coddingtonbear/pomodoro-cube/ArduinoIDE_V2/main/display.cpp

#include "display.h"
#include "nap.h"
#include "consts.h"
#include "indicators.h"
#include "tilt.h"
#include <lvgl.h>
#include <stdio.h>
#include <string.h>
#include <Wire.h>
#include <TFT_eSPI.h>  // By Bodmer V2.5.43

// A TFT_eSPI configured for something other than this panel compiles perfectly
// and then shows nothing at all, which is a miserable thing to debug. Fail at
// build time instead: if this is not set, ArduinoIDE_V2/User_Setup.h has not
// been symlinked into the library. See the README's Building section.
#ifndef GC9A01_DRIVER
#error "TFT_eSPI is not configured for the GC9A01 -- symlink ArduinoIDE_V2/User_Setup.h into ~/Arduino/libraries/TFT_eSPI/"
#endif
#include "src/ui.h"    // SquareLine Studio generated header

// The switch-on prompt's count: Oswald at 150px, the digits 1 and 2 alone. See
// fonts/README.md.
LV_FONT_DECLARE(ui_font_FlipCount);


TFT_eSPI tft = TFT_eSPI();

static lv_disp_draw_buf_t draw_buf;

// Two bands, so LVGL draws the next one while DMA sends the last. Sixty rows
// because that is where taller stopped paying on the board: a leaning face
// redrawn in full took 124 ms in 20-row bands, 89 in 60 and 88 in 120. Each is
// under the 32K pixels a single ESP32-S3 DMA transfer can carry.
constexpr int kBandRows = 60;
static lv_color_t bandA[240 * kBandRows];
static lv_color_t bandB[240 * kBandRows];
lv_disp_drv_t disp_drv;

static bool frameOpen = false;

// Hands each band to DMA and returns at once, which LVGL takes as leave to
// start drawing into the other one. pushImageDMA() waits out the previous
// transfer before it touches the bus, so the bands queue rather than collide.
//
// The transaction is held open from the first band of a frame to the last,
// since closing it waits for DMA and would throw the overlap away. The last
// band closes it, so between frames the bus is idle and the rest of this file
// -- setRotation(), the sleep commands -- can use it without knowing about DMA.
void disp_flush(lv_disp_drv_t *disp, const lv_area_t *area, lv_color_t *color_p) {
  const int32_t w = area->x2 - area->x1 + 1;
  const int32_t h = area->y2 - area->y1 + 1;
  if (!frameOpen) {
    tft.startWrite();
    frameOpen = true;
  }
  tft.pushImageDMA(area->x1, area->y1, w, h, (uint16_t *)&color_p->full);
  if (lv_disp_flush_is_last(disp)) {
    tft.endWrite();
    frameOpen = false;
  }
  lv_disp_flush_ready(disp);
}


namespace {

// Well above hearing, so the backlight never sings, and well within what the
// LED's series resistor and the switching FET will follow.
constexpr int kBacklightFrequency = 5000;
constexpr int kBacklightBits = 8;
// Only used by the 2.x API, which allocates channels by hand. tone() takes
// channel 0, so stay at the other end.
constexpr int kBacklightChannel = 7;

bool backlightIsPwm = false;
int backlightLevel = -1;

void attachBacklightPwm() {
  if (backlightIsPwm) return;
#if ESP_ARDUINO_VERSION_MAJOR >= 3
  ledcAttach(TFT_BL_PIN, kBacklightFrequency, kBacklightBits);
#else
  ledcSetup(kBacklightChannel, kBacklightFrequency, kBacklightBits);
  Nap::keepPwmThroughSleep(kBacklightChannel, kBacklightFrequency, kBacklightBits);
  ledcAttachPin(TFT_BL_PIN, kBacklightChannel);
#endif
  backlightIsPwm = true;
}

// Hand the pin back to plain GPIO so a static level can be held through deep
// sleep. Callers set that level themselves; this only gives them the pin.
void releaseBacklightPwm() {
  if (backlightIsPwm) {
#if ESP_ARDUINO_VERSION_MAJOR >= 3
    ledcDetach(TFT_BL_PIN);
#else
    ledcDetachPin(TFT_BL_PIN);
#endif
    backlightIsPwm = false;
  }
  pinMode(TFT_BL_PIN, OUTPUT);
  backlightLevel = -1;
}

// Give back the two pads holdPausedFrame() latched. Until this runs, nothing
// written to either reaches the pin: gpio_hold_en() survives deep sleep and
// keeps holding after the wake, which is the point of it. Safe when nothing was
// held, so every path that is about to drive the backlight or the reset line
// calls it first rather than reasoning about which sleep it woke from.
void releaseHeldPins() {
  gpio_hold_dis((gpio_num_t)TFT_BL_PIN);
  gpio_hold_dis((gpio_num_t)TFT_RST);
}

// Whether tft.begin() has run this boot. A wake that decides it should go
// straight back to sleep never calls Display::setup(), and still has to be able
// to put the panel away.
bool panelBegun = false;

void beginPanelOnce() {
  if (panelBegun) return;
  tft.begin();
  tft.setRotation(0);  // Let LVGL handle software rotation
  panelBegun = true;
}

// The face last drawn, kept so a change of brightness can repaint it in the
// other scheme without the caller having to hand the timer over again.
Indicators::Ramp lastRamp = Indicators::Ramp::ToGreen;
int lastRampAt = 100;
bool lastFlow = false;
// Whether the timer last drawn was work, which is what the alarm flashes for
// once it has run out: updateTimer() has always drawn the 00:00 before
// cycleTimerFinish() takes the panel.
bool lastWork = true;
bool dimScheme = false;

// A finished timer owns the panel until something ends it, so the ordinary
// repaints stand aside rather than fighting the flash for the background.
bool alerting = false;

// The paused palette is up, and stays up through changes of brightness: a cube
// paused awake dims like any other, and the repaint that goes with dimming
// would otherwise put the running face's colours back on a stopped timer.
bool pausedFrame = false;

// Defined below, once there is an applyPalette() for it to call.
void repaintPalette();

// How the face is turned: the quarter turn the panel is set to, and the whole
// degrees LVGL is drawing on top of it.
int panelQuarter = 0;
int lean = 0;

constexpr lv_coord_t kPanelCentre = 120;

// Turn everything on the face by the lean, about the centre of the panel.
//
// The arc turns itself, by starting its sweep somewhere else. Everything else
// is drawn flat into a layer and turned on the way to the screen, about a pivot
// LVGL measures from the object's own corner -- so the pivot is the centre of
// the panel restated for each object, and has to be restated whenever one
// changes size, which a label does with its text.
void applyLean() {
  // Redraws the whole ring whether or not the angle moved, and refreshLean()
  // comes through here every second while only a label has changed size.
  const uint16_t arcRotation = (uint16_t)((lean + 360) % 360);
  if (reinterpret_cast<lv_arc_t *>(ui_Arc1)->rotation != arcRotation) {
    lv_arc_set_rotation(ui_Arc1, arcRotation);
  }

  lv_obj_update_layout(ui_Screen1);
  lv_obj_t *const leaning[] = {ui_LowBattery, ui_LowBatteryTip, ui_Countdown, ui_BankLabel};
  for (lv_obj_t *obj : leaning) {
    const lv_coord_t pivotX = kPanelCentre - obj->coords.x1;
    const lv_coord_t pivotY = kPanelCentre - obj->coords.y1;
    // Each of these invalidates the object whether or not it changed anything,
    // and most passes change only the angle.
    if (lv_obj_get_style_transform_pivot_x(obj, LV_PART_MAIN) != pivotX) {
      lv_obj_set_style_transform_pivot_x(obj, pivotX, LV_PART_MAIN);
    }
    if (lv_obj_get_style_transform_pivot_y(obj, LV_PART_MAIN) != pivotY) {
      lv_obj_set_style_transform_pivot_y(obj, pivotY, LV_PART_MAIN);
    }
    if (lv_obj_get_style_transform_angle(obj, LV_PART_MAIN) != lean * 10) {
      lv_obj_set_style_transform_angle(obj, (lv_coord_t)(lean * 10), LV_PART_MAIN);
    }
  }
}

// For whatever has just changed the size of something on a leaning face. Does
// nothing on a square one, which is every face at rest.
void refreshLean() {
  if (lean != 0) applyLean();
}

}  // namespace

void Display::finishDrawing() {
  tft.dmaWait();
}

void Display::setBacklight(int percent) {
  if (percent < 0) percent = 0;
  if (percent > 100) percent = 100;
  if (percent == backlightLevel) return;

  attachBacklightPwm();
  const uint32_t duty = (uint32_t)((percent * 255 + 50) / 100);
#if ESP_ARDUINO_VERSION_MAJOR >= 3
  ledcWrite(TFT_BL_PIN, duty);
#else
  ledcWrite(kBacklightChannel, duty);
#endif
  backlightLevel = percent;

  // Dropping the backlight also swaps the scheme: at this brightness a field of
  // colour reads where a thin arc does not. Repaint only on the crossing, so
  // the every-20ms call in loop() stays free.
  const bool dim = percent < BACKLIGHT_FULL_PERCENT;
  if (dim != dimScheme) {
    dimScheme = dim;
    repaintPalette();
  }
}

// LVGL's own image drawing, which drawTransformedWithoutAa() stands in front of.
static void (*drawImgDecoded)(lv_draw_ctx_t *, const lv_draw_img_dsc_t *, const lv_area_t *,
                              const uint8_t *, lv_img_cf_t) = nullptr;

// A leaning face is its labels drawn flat into a layer and then turned, and
// the turn was the bulk of every frame drawn at an angle. Turned without
// anti-aliasing it samples the nearest pixel rather than blending four, at the
// cost of stepped edges on the digits while the cube is off square.
//
// Only transformed draws are touched: the display's own antialiasing flag
// would have done the same for them, but it also rounds off every glyph and
// arc on the panel, square or not.
static void drawTransformedWithoutAa(lv_draw_ctx_t *ctx, const lv_draw_img_dsc_t *dsc,
                                     const lv_area_t *coords, const uint8_t *map, lv_img_cf_t cf) {
  if (dsc->angle == 0 && dsc->zoom == LV_IMG_ZOOM_NONE) {
    drawImgDecoded(ctx, dsc, coords, map, cf);
    return;
  }
  lv_draw_img_dsc_t hard = *dsc;
  hard.antialias = 0;
  drawImgDecoded(ctx, &hard, coords, map, cf);
}

// Whether setup() has run this boot. A switched-off cube brings the panel up to
// count the flips down, and switching it on can then go on to draw a paused
// frame, which asks again; LVGL cannot be initialised twice.
bool displayUp = false;

// The screen showMessage() and showFlipsToGo() put up, while it is up: the text
// of a message or the caption under the count, and the count itself, which is
// hidden for a message.
lv_obj_t *messageScreen = nullptr;
lv_obj_t *messageLabel = nullptr;
lv_obj_t *figureLabel = nullptr;
bool messageInverted = false;

// Push whatever LVGL has pending to the panel now, for the paths that are about
// to block or sleep rather than return to a loop() that would do it.
void pumpLvgl() {
  for (int i = 0; i < 4; i++) {
    Display::render();
    delay(20);
  }
}

void Display::render() {
  // LVGL keeps time only by what it is told. It was told 20 ms a pass, which
  // was true only while a pass was just the delay: once drawing a leaning face
  // took 90 ms of its own, LVGL still saw 20 go by, found its 30 ms refresh
  // period not yet up, and skipped every other pass -- so a frame came about
  // once per two passes plus the drawing, rather than once per pass.
  static uint32_t lastTick = millis();
  const uint32_t now = millis();
  lv_tick_inc(now - lastTick);
  lastTick = now;
  lv_timer_handler();
}

void Display::setup() {
  if (displayUp) return;
  displayUp = true;

  // A paused sleep locks the backlight and the panel's reset line on through
  // deep sleep; release both before driving them again, or tft.begin() cannot
  // reset the panel.
  releaseHeldPins();
  releaseBacklightPwm();
  // Dark until the glass has been wiped. The GC9A01 keeps its frame memory
  // through sleep-in, and through the reset begin() gives it, so bringing the
  // panel up under a lit backlight showed whatever was last drawn before the
  // cube slept -- for the moment it takes LVGL to draw over it.
  digitalWrite(TFT_BL_PIN, LOW);
  // Initialize TFT
  beginPanelOnce();
  tft.fillScreen(TFT_BLACK);
  tft.initDMA();

  // Initialize LVGL
  lv_init();
  lv_disp_draw_buf_init(&draw_buf, bandA, bandB, 240 * kBandRows);
  lv_disp_drv_init(&disp_drv);
  disp_drv.hor_res = 240;
  disp_drv.ver_res = 240;
  disp_drv.flush_cb = disp_flush;
  disp_drv.draw_buf = &draw_buf;

  lv_disp_t *const disp = lv_disp_drv_register(&disp_drv);
  // loop() is what paces redraws, a pass at least LOOP_PASS_MS apart, so LVGL
  // should draw whenever a pass asks. Its own default of 30 ms skipped every
  // other pass once a frame at an angle came in under that.
  lv_timer_set_period(disp->refr_timer, LOOP_PASS_MS / 2);
  drawImgDecoded = disp->driver->draw_ctx->draw_img_decoded;
  disp->driver->draw_ctx->draw_img_decoded = drawTransformedWithoutAa;

  ui_init();

  // PWM only once TFT_eSPI has finished with the pin. It leaves TFT_BL alone
  // unless TFT_BACKLIGHT_ON is defined, which tft_setup.h does not define -- but
  // an LEDC channel it did clobber would be silently stuck, and attaching after
  // begin() costs nothing to rule that out.
  //
  // At nothing, and after the face exists, since a change of level repaints
  // it. Whoever draws the first frame lights it: loop() does at the end of
  // every pass, and the paths that never reach loop() do for themselves.
  // Wiping the glass first was not enough on the board, where the last frame
  // still showed for a moment.
  Display::setBacklight(0);
}


// Checked first for the same reason as the style setters below: showing an
// object redraws the whole of it even when it was already showing, and the
// arc's whole is most of the panel.
static void show(lv_obj_t *obj, bool visible) {
  if (visible == !lv_obj_has_flag(obj, LV_OBJ_FLAG_HIDDEN)) return;
  if (visible) lv_obj_clear_flag(obj, LV_OBJ_FLAG_HIDDEN);
  else lv_obj_add_flag(obj, LV_OBJ_FLAG_HIDDEN);
}

void Display::updateBattery(float voltage) {
  // Printed with %d rather than %.2f: lv_snprintf only handles floats when
  // LV_SPRINTF_USE_FLOAT is set, which is off by default and lives in an
  // lv_conf.h this repo doesn't control.
  const int centivolts = (int)(voltage * 100.0f + 0.5f);
  lv_label_set_text_fmt(ui_LowBatteryVoltage, "%d.%02d", centivolts / 100, centivolts % 100);

  // Nothing on screen at all until the charge is actually worth acting on.
  const bool warn = Indicators::showLowBattery(voltage);
  show(ui_LowBattery, warn);
  show(ui_LowBatteryTip, warn);
  refreshLean();
}

// Style setters that leave an object alone when it already has the value.
//
// LVGL redraws an object whenever one of its styles is set, whether or not the
// value changed, and the face is repainted from scratch every second. Setting
// the screen's background that way redrew all 240x240 pixels once a second, a
// frame that takes long enough to cross the SPI bus that it could be seen
// arriving in bands. Skipping the no-ops leaves the tick redrawing only the
// digits and the part of the arc that moved.
static void setColor(lv_obj_t *obj, lv_style_prop_t prop, uint32_t color, lv_part_t part) {
  const lv_color_t c = lv_color_hex(color);
  if (lv_obj_get_style_prop(obj, part, prop).color.full == c.full) return;
  lv_style_value_t v;
  v.color = c;
  lv_obj_set_local_style_prop(obj, prop, v, part);
}

static void setOpa(lv_obj_t *obj, lv_style_prop_t prop, lv_opa_t opa, lv_part_t part) {
  if (lv_obj_get_style_prop(obj, part, prop).num == opa) return;
  lv_style_value_t v;
  v.num = opa;
  lv_obj_set_local_style_prop(obj, prop, v, part);
}

// Paint the arc and its knob in one colour, at one opacity.
static void setArcAppearance(uint32_t color, lv_opa_t opa) {
  setColor(ui_Arc1, LV_STYLE_ARC_COLOR, color, LV_PART_INDICATOR);
  setOpa(ui_Arc1, LV_STYLE_ARC_OPA, opa, LV_PART_INDICATOR);
  setColor(ui_Arc1, LV_STYLE_BG_COLOR, color, LV_PART_KNOB);
  setOpa(ui_Arc1, LV_STYLE_BG_OPA, opa, LV_PART_KNOB);
}

// The low-battery outline is three objects with three different style
// properties, which is why it needs its own pass rather than joining the labels.
static void setBatteryColor(uint32_t color) {
  setColor(ui_LowBattery, LV_STYLE_BORDER_COLOR, color, LV_PART_MAIN);
  setColor(ui_LowBatteryTip, LV_STYLE_BG_COLOR, color, LV_PART_MAIN);
  setColor(ui_LowBatteryVoltage, LV_STYLE_TEXT_COLOR, color, LV_PART_MAIN);
}

// Paint every colour on the panel at once, so a swap can't half-apply.
static void applyPalette(const Indicators::Palette &p) {
  setColor(ui_Screen1, LV_STYLE_BG_COLOR, p.background, LV_PART_MAIN);
  setColor(ui_Arc1, LV_STYLE_ARC_COLOR, p.track, LV_PART_MAIN);
  lv_obj_t *const labels[] = {ui_Countdown, ui_BankLabel};
  for (lv_obj_t *label : labels) {
    setColor(label, LV_STYLE_TEXT_COLOR, p.text, LV_PART_MAIN);
  }
  setArcAppearance(p.arc, LV_OPA_COVER);
  setBatteryColor(p.battery);
}

namespace {

void repaintPalette() {
  if (alerting || pausedFrame) return;
  applyPalette(Indicators::palette(lastRamp, lastRampAt, lastFlow, dimScheme));
}

}  // namespace

void Display::deepSleep() {
  // Both of these were no-ops when the last sleep held a frame: the pads were
  // still latched, so the backlight stayed on at full for the whole of the next
  // sleep. A cube parked face up and then turned face down went dark on the
  // outside and burned the pack on the inside.
  releaseHeldPins();
  releaseBacklightPwm();
  digitalWrite(TFT_BL_PIN, LOW);
  // Reached on a wake that went straight back to sleep without ever bringing
  // the display up, in which case there is no SPI to send a command over yet --
  // and a panel left holding a frame is still refreshing one, at a few
  // milliamps, which is an order above what the rest of the cube draws asleep.
  // The backlight is already off, so none of this is seen.
  beginPanelOnce();
  // Send GC9A01 Sleep In command
  tft.writecommand(0x10);
  delay(120); // Required transition delay for the controller to power down
}

void Display::holdPausedFrame() {
  // No Sleep In command: the panel keeps refreshing the frame from its own
  // memory, and holding the pin keeps it lit once the CPU stops.
  //
  // The reset line has to be held too. esp_deep_sleep_start() returns every pad
  // that is not held to its default -- high impedance -- and a floating RST on
  // the GC9A01 drifts low within seconds, which resets the controller, clears
  // its frame memory and drops it back into sleep-in. That is what blanked the
  // paused frame a few seconds after the cube was set down: the backlight was
  // still on, there was just nothing left on the panel to light.
  //
  // Full brightness, not the idle level, and not a choice: nothing is left
  // running to generate PWM once the CPU stops, and gpio_hold_en() freezes the
  // instantaneous level rather than the duty cycle. A parked cube is therefore
  // lit at full or not at all -- turning it face down is how you turn it off.
  // Deliberately does *not* release the holds first. When they are already on,
  // they are already holding exactly the levels this function is about to ask
  // for, so releasing them buys nothing -- and it hands the reset line back to
  // an output register that waking from deep sleep has cleared to zero. The pad
  // then presents a LOW for as long as it takes to get round to writing it
  // again, which is a reset pulse: the GC9A01 clears its frame memory and drops
  // into sleep-in, and the backlight goes on being held up over a blank panel.
  // That is the same symptom the held reset line was introduced to fix, put
  // back by the release that was supposed to make this path safe.
  releaseBacklightPwm();
  digitalWrite(TFT_BL_PIN, HIGH);
  gpio_hold_en((gpio_num_t)TFT_BL_PIN);

  // Level before direction, for the same reason: this writes the output
  // register while the pad is still an input, so changing the direction takes
  // it straight to HIGH rather than through whatever the register held.
  digitalWrite(TFT_RST, HIGH);
  pinMode(TFT_RST, OUTPUT);
  gpio_hold_en((gpio_num_t)TFT_RST);
}

void Display::showPaused() {
  // Back to the dark palette whether the pause caught a countdown or a flow
  // stint, and whether the panel was dim or bright: paused has to look like one
  // thing, awake and dimmed or asleep and held at full. Neither has any
  // business with a half-finished flash, which would otherwise be the frame
  // left lit on the panel for as long as the cube sits there.
  alerting = false;
  pausedFrame = true;
  show(ui_Arc1, true);
  applyPalette({SCREEN_BG_COLOR, COUNTDOWN_COLOR_PAUSED, ARC_COLOR_PAUSED, ARC_TRACK_COLOR,
                LOW_BATTERY_COLOR});

  // The frame has to reach the panel before the CPU stops, so pump LVGL rather
  // than waiting for the next loop() that will never come.
  pumpLvgl();
}

// Puts the message screen up if it is not already. A screen of its own rather
// than labels over the face: nothing of the timer belongs on it, and dropping it
// afterwards leaves the face as it was.
void ensureMessageScreen() {
  Display::setup();
  if (messageScreen) return;
  messageScreen = lv_obj_create(NULL);
  lv_obj_set_style_bg_opa(messageScreen, LV_OPA_COVER, LV_PART_MAIN);

  messageLabel = lv_label_create(messageScreen);
  lv_obj_set_style_text_font(messageLabel, &lv_font_montserrat_20, LV_PART_MAIN);
  lv_obj_set_style_text_align(messageLabel, LV_TEXT_ALIGN_CENTER, LV_PART_MAIN);
  lv_label_set_text(messageLabel, "");

  figureLabel = lv_label_create(messageScreen);
  lv_obj_set_style_text_font(figureLabel, &ui_font_FlipCount, LV_PART_MAIN);
  lv_label_set_text(figureLabel, "");
  lv_obj_add_flag(figureLabel, LV_OBJ_FLAG_HIDDEN);

  lv_scr_load(messageScreen);
}

// Colours the message screen and pushes it out. Nothing is running loop()
// while one of these is up, so the frame has to be pushed out here or it never
// reaches the glass.
void presentMessageScreen(bool inverted) {
  messageInverted = inverted;
  const lv_color_t bg = inverted ? lv_color_white() : lv_color_black();
  const lv_color_t fg = inverted ? lv_color_black() : lv_color_white();
  lv_obj_set_style_bg_color(messageScreen, bg, LV_PART_MAIN);
  lv_obj_set_style_text_color(messageLabel, fg, LV_PART_MAIN);
  lv_obj_set_style_text_color(figureLabel, fg, LV_PART_MAIN);
  pumpLvgl();
  Display::setBacklight(BACKLIGHT_FULL_PERCENT);
}

void Display::showMessage(const char *text, bool inverted) {
  ensureMessageScreen();
  const bool figureShown = !lv_obj_has_flag(figureLabel, LV_OBJ_FLAG_HIDDEN);
  if (!figureShown && strcmp(lv_label_get_text(messageLabel), text) == 0 &&
      messageInverted == inverted) {
    return;
  }

  lv_obj_add_flag(figureLabel, LV_OBJ_FLAG_HIDDEN);
  lv_label_set_text(messageLabel, text);
  lv_obj_center(messageLabel);
  presentMessageScreen(inverted);
}

void Display::showFlipsToGo(int flips) {
  ensureMessageScreen();
  char figure[12];
  snprintf(figure, sizeof figure, "%d", flips);
  const bool figureShown = !lv_obj_has_flag(figureLabel, LV_OBJ_FLAG_HIDDEN);
  if (figureShown && strcmp(lv_label_get_text(figureLabel), figure) == 0 && !messageInverted) {
    return;
  }

  // The figure a little above centre and the caption under it, so the pair sits
  // centred on the round panel together rather than the figure alone.
  lv_obj_clear_flag(figureLabel, LV_OBJ_FLAG_HIDDEN);
  lv_label_set_text(figureLabel, figure);
  lv_obj_align(figureLabel, LV_ALIGN_CENTER, 0, -22);
  lv_label_set_text(messageLabel, "to go");
  lv_obj_align_to(messageLabel, figureLabel, LV_ALIGN_OUT_BOTTOM_MID, 0, 8);
  presentMessageScreen(false);
}

void Display::hideMessage() {
  if (!messageScreen) return;
  lv_scr_load(ui_Screen1);
  lv_obj_del(messageScreen);
  messageScreen = nullptr;
  messageLabel = nullptr;
  figureLabel = nullptr;
}

void Display::setAngle(float degrees) {
  const Tilt::Split split = Tilt::split(degrees);

  if (split.quarter != panelQuarter) {
    panelQuarter = split.quarter;
    // Changes where writes land, not what is already on the glass, so the old
    // frame stands until the new one is drawn over it.
    tft.setRotation(split.quarter);
    lv_obj_invalidate(lv_scr_act());
  }

  if (split.lean != lean) {
    lean = split.lean;
    applyLean();
  }
}

void Display::rotateScreen(Orientation ori) {
  Display::setAngle(Tilt::faceAngle(ori));
}

static void setCountdownText(int seconds) {
  lv_label_set_text(ui_Countdown, Indicators::clockText(seconds).text);
}

// The bank in the smallest form that stays unambiguous: no marker to explain,
// because minutes and seconds are shown as such and hours only appear when
// there are some.
static void setBankText(int seconds) {
  if (seconds < 0) seconds = 0;
  if (seconds >= 3600) {
    lv_label_set_text_fmt(ui_BankLabel, "BANK %d:%02d:%02d", seconds / 3600,
                          (seconds % 3600) / 60, seconds % 60);
  } else {
    lv_label_set_text_fmt(ui_BankLabel, "BANK %d:%02d", seconds / 60, seconds % 60);
  }
}

void Display::updateTimer(const TimerView &view) {
  // Whatever brought us here ended the alarm: a new face, or a timer with
  // seconds on it again. Take the ring back before anything is painted.
  alerting = false;
  pausedFrame = false;
  show(ui_Arc1, true);

  setCountdownText(view.seconds);

  // The bank belongs on the work face: on the break face the big number already
  // is the bank, counting down.
  const bool showBank = view.flow && view.countingUp;
  if (showBank) setBankText(view.bankSeconds);
  show(ui_BankLabel, showBank);

  // Counting up has no total to drain against, so the arc fills as a lap
  // indicator, its colour running the ramp over what is left of the lap.
  const int remaining = view.countingUp ? Indicators::lapPercent(view.seconds)
                                        : Indicators::remainingPercent(view.seconds, view.selSeconds);
  lastRamp = Indicators::rampFor(view.work, view.countingUp, view.seconds);
  lastRampAt = view.countingUp ? 100 - remaining : remaining;
  lastFlow = view.flow;
  lastWork = view.work;
  lv_arc_set_value(ui_Arc1, remaining);

  // Repaints every colour from scratch, which also undoes showPaused() without
  // needing to know whether it ran.
  repaintPalette();

  refreshLean();
}

unsigned long lastFinishChange = 0;
bool finishInverted = false;

void Display::cycleTimerFinish() {
  const unsigned long now = millis();

  // Called every pass while the timer sits at zero, and self-timed, so the
  // flash keeps its own cadence rather than the motor's.
  if (alerting) {
    if (now - lastFinishChange < (unsigned long)ALERT_FLASH_MS) return;
    finishInverted = !finishInverted;
  } else {
    // First pass of an alarm: take the panel, and start on the dark half so the
    // flash reads as something arriving rather than something leaving.
    alerting = true;
    finishInverted = false;
    show(ui_Arc1, false);
  }

  applyPalette(Indicators::alertPalette(finishInverted, lastWork));
  lastFinishChange = now;
}
