coddingtonbear/pomodoro-cube/ArduinoIDE_V2/main/ble.h

#pragma once
#include "bthome.h"

// The radio half of the BTHome broadcast: takes the payload bthome.cpp builds
// and puts it on the air over NimBLE.
//
// Advertising only -- there is no GATT server, no scanning and nothing to
// connect to. A BTHome device is a beacon, and a non-connectable advertisement
// is a millisecond of radio at a time, sent in short bursts.
namespace BLE {

// Puts the cube on the air. The controller itself is brought up by the first
// burst and stays up until shutdown(); only advertising starts and stops with
// each burst. Bringing it up blocks while the NimBLE host syncs, which the
// trace reports.
void setup();

// Offer the current state. Cheap enough to call on every pass of the loop: the
// radio only goes on the air when BTHome::Scheduler says a burst is due, and
// this is also what takes it off again once the burst has run. Does nothing
// before setup().
void publish(const BTHome::State &state);

// Puts the advertisement that goes out as the cube falls asleep on the air,
// with connectivity and running both dropped -- see
// BTHome::Sequencer::farewell() -- at the fastest interval a legacy
// advertisement allows, and returns at once. The radio keeps repeating it
// through whatever shutdown work follows, until shutdown() is called; the
// farewell cannot be repeated later, so every copy that gets out is one the
// receiver might not otherwise have heard.
//
// Safe to call when BLE was never brought up, which is the path a cube takes
// when it wakes on a resting face and goes straight back to sleep.
void farewell();

// Shuts the controller down. Call it last, immediately before deep sleep: it
// first makes sure a farewell put on the air by farewell() has had at least
// FAREWELL_MIN_AIRTIME_MS to repeat, blocking for the remainder if the work in
// between was quicker than that, so the guarantee does not depend on how long
// the panel and motor happen to take. Deep sleep cuts the radio's power
// anyway; shutting it down in order means the controller is not
// mid-transmission when that happens.
//
// Safe to call when BLE was never brought up.
void shutdown();

// Whether a burst or the farewell is on the air. The CPU does not light-sleep
// under one -- the controller is built without the sleep support that would
// let advertising and light sleep coexist.
bool onAir();

// The least time a farewell is on the air before shutdown() lets the radio go.
// The shutdown work it overlaps -- putting the panel away, the second's pause,
// the shutdown buzz -- takes longer than this in practice; the figure is a
// floor, not the expectation.
constexpr unsigned long FAREWELL_MIN_AIRTIME_MS = 1000;

}  // namespace BLE
