coddingtonbear/pomodoro-cube/ArduinoIDE_V2/main/util.cpp

#include "util.h"
#include <Arduino.h>
#include <math.h>
#include "consts.h"
#include "battery.h"
#include "util.h"
#include "qmi.h"
#include "display.h"
#include <driver/rtc_io.h>
#include "vFilter.h"
#include "haptic.h"
#include "ble.h"

VoltageSmoother<10> vFilter;


void Util::updateBattery() {
  vFilter.add(Battery::getVoltage());
  Display::updateBattery(vFilter.getAverage());
}

float Util::batteryVolts() {
  return vFilter.getAverage();
}

Orientation Util::calcOrientation(float ax, float ay, float az) {
  // Whichever axis carries the most of gravity names the face. The signs are
  // verified on hardware: the QMI8658's +Z points into the back of the cube,
  // not out of the front, so a cube resting screen-up reads -1g on Z.
  //
  // This used to test each axis against a fixed +-0.8, and fall through to
  // DEG_0 when nothing matched. That left a dead zone covering every attitude
  // more than about 37 degrees off an axis, and the fall-through reported a
  // timer face rather than admitting it did not know -- so a board resting at
  // an angle ran a 25-minute timer it had never been put on. In a
  // fifteen-minute trace from the board, 38.8% of all samples landed in that
  // dead zone. A dominant axis has no dead zone: every reading names a face,
  // and readings too close to call are screened out by isDecisive() instead of
  // being quietly answered wrong.
  const float mx = fabsf(ax);
  const float my = fabsf(ay);
  const float mz = fabsf(az);

  if (mz >= mx && mz >= my) return az > 0 ? Orientation::FACE_DOWN : Orientation::FACE_UP;
  if (mx >= my) return ax > 0 ? Orientation::DEG_180 : Orientation::DEG_0;
  return ay > 0 ? Orientation::DEG_270 : Orientation::DEG_90;
}

bool Util::isGravityOnly(float ax, float ay, float az) {
  const float magnitude = sqrtf(ax * ax + ay * ay + az * az);
  return magnitude >= ORI_GRAVITY_MIN_G && magnitude <= ORI_GRAVITY_MAX_G;
}

bool Util::isDecisive(float ax, float ay, float az) {
  float mx = fabsf(ax);
  float my = fabsf(ay);
  float mz = fabsf(az);

  // The top two, without sorting all three.
  float first = mx, second = my;
  if (second > first) { const float swap = first; first = second; second = swap; }
  if (mz > first) { second = first; first = mz; }
  else if (mz > second) { second = mz; }

  return first - second >= ORI_DOMINANCE_MARGIN_G;
}


void Util::deepSleep(SleepMode mode, bool announce) {
  // Before anything else that takes time: Home Assistant holds the last state
  // it heard, so a cube that just stopped counting has to say so while it still
  // has a radio. This only puts the farewell on the air; the radio goes on
  // repeating it through everything below and is shut down last, so the
  // second's pause doubles as airtime for the one advertisement that cannot be
  // sent again.
  BLE::farewell();

  // Whatever the motor was part-way through ends here: nothing below returns to
  // loop() to finish it, and a motor left running would be the movement that
  // wakes the cube straight back up.
  Haptic::stop();

  // Ahead of the pause below rather than after it, so the motor has that second
  // to spin down before the wake-on-motion detector is armed.
  if (announce) Haptic::playBlocking(Haptic::Pattern::FaceChange);

  // Written down rather than worked out again on the next wake. A wake that
  // goes straight back to sleep never brings the panel up, so it cannot ask the
  // panel what it is showing -- and the two answers need different handling:
  // a held frame has to be put away before the panel can go dark, and a blank
  // panel has to be drawn on before the backlight is worth holding up.
  RtcState::data().panelHoldingFrame = (mode == SleepMode::Paused);

  if (mode == SleepMode::Off) Display::deepSleep();
  else Display::holdPausedFrame();

  delay(1000);

  QMI::setupWakeup();

  // Float I2C lines to prevent parasitic draw
  pinMode(I2C_SDA_PIN, INPUT);
  pinMode(I2C_SCL_PIN, INPUT);

  rtc_gpio_pullup_dis(IMU_INT_PIN);
  rtc_gpio_pulldown_en(IMU_INT_PIN);

  esp_sleep_enable_ext0_wakeup(IMU_INT_PIN, 1);  // 1 = Wakeup at HIGH

  Haptic::holdForSleep();

  // Last, so the farewell has had the whole of the above to repeat.
  BLE::shutdown();

  esp_deep_sleep_start();
}

bool Util::isRestingFace(Orientation ori) {
  return ori == Orientation::FACE_UP || ori == Orientation::FACE_DOWN;
}

Util::RestPlan Util::restOnFace(RtcState::Data &data, Orientation ori, Orientation timerFace,
                                int remaining, int selected, bool countingUp) {
  // Park rather than discard, on either face. Setting the cube down is not the
  // same as choosing a different interval -- that is what standing it on another
  // face means -- so the pause and the break bank both survive it. Face down is
  // face up with the lights out.
  RtcState::storePause(data, timerFace, remaining, selected, countingUp);

  // Face down is also off, which is the one thing that tells the two faces
  // apart after the lights: a cube put away face down stays down until it is
  // deliberately switched back on, however much it is jostled.
  const bool lit = ori == Orientation::FACE_UP;
  data.switchedOff = !lit;
  return {lit, lit ? SleepMode::Paused : SleepMode::Off};
}

void Util::parkFreshTimer(RtcState::Data &data) {
  if (RtcState::hasPause(data)) return;
  RtcState::storePause(data, Orientation::DEG_0, TIMER_WORK_SECONDS, TIMER_WORK_SECONDS, false);
}

int Util::backlightPercent(const BacklightView &view) {
  // Just set down. The face was chosen a moment ago, and what it came up with is
  // the answer to that choice.
  if (view.sinceFaceChangeMs < (unsigned long)BACKLIGHT_ATTENTION_SECONDS * 1000UL) {
    return BACKLIGHT_FULL_PERCENT;
  }

  // Just tapped, which is the same request made deliberately: someone wants to
  // read a face that has settled to the idle level. Held longer than a face
  // change, because they are coming to it cold rather than already looking.
  if (view.sinceTapMs < (unsigned long)BACKLIGHT_TAP_SECONDS * 1000UL) {
    return BACKLIGHT_FULL_PERCENT;
  }

  // Running out, or run out. The same test covers both: a countdown at 0 has
  // finished and is buzzing, and stays lit until it is dealt with -- which is
  // bounded, because a finished timer sleeps the cube after thirty seconds.
  //
  // Not while paused: a countdown parked with four seconds left is not about
  // to do anything, and would otherwise hold the panel at full for as long as
  // it lay there.
  if (!view.paused && !view.countingUp &&
      view.remainingSeconds <= BACKLIGHT_ATTENTION_SECONDS) {
    return BACKLIGHT_FULL_PERCENT;
  }

  // A flow lap closing, from a moment before to a moment after: the arc comes
  // round, a pomodoro is scored, and the colour snaps to the next lap's. Not
  // the start of the first lap, which is no closing at all -- and is lit
  // anyway, as the face change it is.
  if (!view.paused && view.countingUp && view.remainingSeconds >= 0) {
    const unsigned long lapMs = (unsigned long)FLOW_LAP_SECONDS * 1000UL;
    const unsigned long elapsedMs = (unsigned long)view.remainingSeconds * 1000UL +
                                    (view.sinceTickMs < 1000UL ? view.sinceTickMs : 999UL);
    const unsigned long intoLap = elapsedMs % lapMs;
    const bool closing = intoLap >= lapMs - BACKLIGHT_LAP_MS;
    const bool closed = elapsedMs >= lapMs && intoLap < BACKLIGHT_LAP_MS;
    if (closing || closed) return BACKLIGHT_FULL_PERCENT;
  }

  return BACKLIGHT_IDLE_PERCENT;
}

uint32_t Util::cpuMhz(int backlightPercent) {
  return backlightPercent >= BACKLIGHT_FULL_PERCENT ? CPU_MHZ_LIT : CPU_MHZ_IDLE;
}

bool Util::loopIsIdle(const PaceView &view) {
  // Lit is when someone is looking, and the angle is being followed at the
  // rate it was tuned for; busy is timing that is finer than an idle pass.
  return view.backlightPercent < BACKLIGHT_FULL_PERCENT && !view.busy &&
         view.sinceMovedMs >= LOOP_STILL_HOLD_MS;
}

uint32_t Util::loopPassMs(const PaceView &view) {
  if (!loopIsIdle(view)) return LOOP_PASS_MS;
  // On the tick rather than late for it. At least a millisecond, so a tick
  // that is due now is taken by the very next pass.
  if (view.untilTickMs < LOOP_IDLE_PASS_MS) {
    return view.untilTickMs == 0 ? 1 : (uint32_t)view.untilTickMs;
  }
  return LOOP_IDLE_PASS_MS;
}

Util::TimerSpec Util::getTimerSpec(Orientation ori, int bankedBreakSeconds) {
  switch (ori) {
    case Orientation::DEG_0:
      return {TimerKind::Work, TimerMode::Countdown, TIMER_WORK_SECONDS, false, false};
    case Orientation::DEG_90:
      return {TimerKind::Break, TimerMode::Countdown, TIMER_SHORT_BREAK_SECONDS, false, false};
    case Orientation::DEG_180:
      // Flow's work face: no length, because it counts up until the cube is
      // turned off it.
      return {TimerKind::Work, TimerMode::CountUp, 0, true, false};
    case Orientation::DEG_270:
      // Flow's break face pays out the bank and nothing else. An empty bank is
      // a break of no length, which finishes the moment it starts -- there is
      // nothing to fall back on, because any fallback would be break time
      // nobody worked for.
      return {TimerKind::Break, TimerMode::Countdown,
              bankedBreakSeconds > 0 ? bankedBreakSeconds : 0, true, true};
    default:
      // A resting face runs no timer, but must still not report zero: a
      // zero-length timer would divide by zero in the arc.
      return {TimerKind::Work, TimerMode::Countdown, TIMER_WORK_SECONDS, false, false};
  }
}

int Util::flowBreakCredit(int workedSeconds) {
  if (workedSeconds <= 0) return 0;
  return workedSeconds / FLOW_BREAK_DIVISOR;
}

int Util::flowBankPreview(int bankedSeconds, int elapsedSeconds) {
  if (bankedSeconds < 0) bankedSeconds = 0;
  return bankedSeconds + flowBreakCredit(elapsedSeconds);
}

bool Util::completesFlowLap(int elapsedSeconds) {
  return elapsedSeconds > 0 && elapsedSeconds % FLOW_LAP_SECONDS == 0;
}

Util::SwitchOnListener::SwitchOnListener(unsigned long nowMs)
    : deadline_(nowMs + SWITCH_ON_FLIP_WINDOW_MS), lastDisturbed_(nowMs) {}

Util::SwitchOnListener::Side Util::SwitchOnListener::sideOf(float ax, float ay, float az) {
  const float magnitude = sqrtf(ax * ax + ay * ay + az * az);
  if (magnitude < FLIP_MAGNITUDE_MIN_G || magnitude > FLIP_MAGNITUDE_MAX_G) return Side::Neither;
  // +Z points into the back of the cube; see calcOrientation().
  if (az <= -FLIP_SIDE_MIN_G) return Side::Up;
  if (az >= FLIP_SIDE_MIN_G) return Side::Down;
  return Side::Neither;
}

Util::SwitchOnVerdict Util::SwitchOnListener::update(bool haveReading, float ax, float ay,
                                                     float az, unsigned long nowMs) {
  if (haveReading) {
    updateOriDebounce(ax, ay, az, nowMs);

    // A side counts once it has held for FLIP_HOLD_MS, and a flip is the cube
    // coming to face up from face down. Going face up again without having
    // been face down in between is not another flip, and nor is a side face:
    // standing the cube on a timer face and back is a quarter turn, not a flip.
    const Side reading = sideOf(ax, ay, az);
    if (reading != candidate_) {
      candidate_ = reading;
      candidateSince_ = nowMs;
    } else if (reading != Side::Neither && reading != side_ &&
               nowMs - candidateSince_ >= FLIP_HOLD_MS) {
      side_ = reading;
      if (side_ == Side::Up) {
        if (++flips_ >= SWITCH_ON_FLIPS) return SwitchOnVerdict::On;
        deadline_ = nowMs + SWITCH_ON_FLIP_WINDOW_MS;
      }
    }
  }

  const Orientation face = getDebouncedOriState();
  const bool resting = haveReading && isGravityOnly(ax, ay, az) &&
                       calcOrientation(ax, ay, az) == face;
  if (!resting) lastDisturbed_ = nowMs;

  // Left lying on some other face before it was ever flipped: not being
  // switched on, so no reason to wait out the window.
  if (flips_ == 0 && face != Orientation::FACE_UP && face != Orientation::UNDEFINED &&
      nowMs - lastDisturbed_ >= SWITCH_ON_GIVE_UP_MS) {
    return SwitchOnVerdict::StayOff;
  }
  if ((long)(nowMs - deadline_) >= 0) return SwitchOnVerdict::StayOff;
  return SwitchOnVerdict::Listening;
}

// The face the cube is currently being read as, and the one it has been read as
// for long enough to believe.
Orientation candidateState = Orientation::UNDEFINED;
unsigned long candidateSince = 0;
Orientation debouncedState = Orientation::UNDEFINED;

bool Util::updateOriDebounce(float ax, float ay, float az, unsigned long nowMs) {
  Orientation rawState = Orientation::UNDEFINED;
  if (isGravityOnly(ax, ay, az)) {
    const Orientation face = calcOrientation(ax, ay, az);
    // An attitude poised between two faces may go on confirming the face the
    // cube is already believed to be on, but is never enough to move it onto a
    // new one. UNDEFINED here means "no opinion", which restarts the clock
    // below rather than being accepted as a face of its own.
    //
    // Unless no face is believed yet, in which case the best available answer
    // is taken however narrow its lead. The margin exists to stop a cube
    // alternating between two faces, and that needs an incumbent to alternate
    // with; with nothing to protect it only withholds an answer. Measured on
    // the board: a bare disc leaned against something rests at 46 degrees, four
    // hundredths of a g off the halfway line, and stayed awake for nineteen
    // seconds showing no timer at all rather than committing to a face. Once a
    // face is accepted the margin holds it there, so a narrow call is made once
    // and then stands.
    if (debouncedState == Orientation::UNDEFINED || face == debouncedState ||
        isDecisive(ax, ay, az)) {
      rawState = face;
    }
  }

  // Any change of reading restarts the clock. The earlier version timed from
  // the last sample that agreed with the *accepted* face instead, which means a
  // cube tumbling through three faces on its way to a fourth never reset it:
  // whatever sample happened to land ORI_DEBOUNCE_DELAY after the cube left the
  // old face was taken as the new one. Picking a cube up off its face-up rest
  // and standing it on a timer face goes through face-up on the way, so that is
  // exactly how a cube ended up believing it had been set down again, parking
  // the paused frame on a panel that should have gone back to work.
  if (rawState != candidateState) {
    candidateState = rawState;
    candidateSince = nowMs;
    return false;
  }

  if (rawState == Orientation::UNDEFINED) return false;
  if (rawState == debouncedState) return false;
  if (nowMs - candidateSince < (unsigned long)ORI_DEBOUNCE_DELAY) return false;

  debouncedState = rawState;
  return true;
}

Orientation Util::getDebouncedOriState() {
  return debouncedState;
}

void Util::resetOriDebounce() {
  candidateState = Orientation::UNDEFINED;
  candidateSince = 0;
  debouncedState = Orientation::UNDEFINED;
}
