coddingtonbear/pomodoro-cube/sim/tests/test_bthome.cpp

// Tests for the BTHome v2 encoder. These assert exact bytes rather than round
// tripping through the encoder's own logic: the whole point is that a receiver
// that has never seen this code can read the result.
#include "bthome.h"

#include <cstring>

#include "check.h"
#include "consts.h"

namespace {

BTHome::State workTimerRunning() {
  BTHome::State state;
  state.packetId = 7;
  state.batteryVolts = 3.82f;
  state.awake = true;
  state.running = true;
  state.work = true;
  state.pomodoroCount = 3;
  state.remainingSeconds = 1234;
  state.selectedSeconds = 1500;
  return state;
}

// Flags is 3 bytes; then the service data's length, type, 2 UUID bytes and the
// device info byte. Objects start after that.
constexpr size_t OBJECTS_START = 3 + 1 + 1 + 2 + 1;

size_t valueSizeOf(uint8_t id) {
  switch (id) {
    case 0x00: case 0x0F: case 0x19: case 0x27: return 1;  // uint8 and binaries
    case 0x0C: case 0x3D: return 2;             // uint16
    case 0x42: return 3;                        // uint24
    default: return 0;                          // unknown
  }
}

// Walks the object section, so ordering can be checked without hardcoding it.
size_t objectIdsOf(const uint8_t *advert, size_t length, uint8_t *ids, size_t max) {
  size_t offset = OBJECTS_START;
  size_t count = 0;

  while (offset < length && count < max) {
    const uint8_t id = advert[offset];
    const size_t size = valueSizeOf(id);
    if (size == 0) return count;

    ids[count++] = id;
    offset += 1 + size;
  }
  return count;
}

// The value bytes of the nth object with this id, or nullptr. Scanning beats
// hardcoded offsets: the first draft of these tests counted by hand and got
// every offset one byte low.
const uint8_t *findObject(const uint8_t *advert, size_t length, uint8_t wanted,
                          size_t occurrence = 0) {
  size_t offset = OBJECTS_START;
  size_t seen = 0;

  while (offset < length) {
    const uint8_t id = advert[offset];
    const size_t size = valueSizeOf(id);
    if (size == 0) return nullptr;

    if (id == wanted && seen++ == occurrence) return advert + offset + 1;
    offset += 1 + size;
  }
  return nullptr;
}

}  // namespace

void testEncodesKnownStateExactly() {
  uint8_t advert[BTHome::MAX_ADVERTISEMENT];
  const size_t length = BTHome::encode(workTimerRunning(), advert, sizeof(advert));

  const uint8_t expected[] = {
      0x02, 0x01, 0x06,              // Flags: LE general discoverable, BR/EDR not supported
      0x1A, 0x16, 0xD2, 0xFC, 0x44,  // 26 bytes of service data, UUID 0xFCD2, BTHome v2 trigger based
      0x00, 0x07,                    // packet id 7
      0x0C, 0xEC, 0x0E,              // voltage 3820 mV
      0x0F, 0x01,                    // work rather than break
      0x19, 0x01,                    // connectivity: awake
      0x27, 0x01,                    // running
      0x3D, 0x03, 0x00,              // 3 pomodoros
      0x42, 0x50, 0xD4, 0x12,        // remaining 1_234_000 ms
      0x42, 0x60, 0xE3, 0x16,        // started at 1_500_000 ms
  };

  CHECK(length == sizeof(expected));
  CHECK(std::memcmp(advert, expected, sizeof(expected)) == 0);
}

void testFitsInALegacyAdvertisement() {
  BTHome::State state = workTimerRunning();
  state.packetId = 255;
  state.pomodoroCount = 65535;
  state.batteryVolts = 4.2f;
  state.remainingSeconds = 12 * 60 * 60;
  state.selectedSeconds = 12 * 60 * 60;

  uint8_t advert[BTHome::MAX_ADVERTISEMENT];
  const size_t length = BTHome::encode(state, advert, sizeof(advert));

  CHECK(length > 0);
  CHECK(length <= BTHome::MAX_ADVERTISEMENT);
}

void testObjectIdsAscend() {
  // The spec requires ascending object ids, and a receiver may reject a packet
  // that breaks it. Repeated ids are allowed, so this is non-decreasing.
  uint8_t advert[BTHome::MAX_ADVERTISEMENT];
  const size_t length = BTHome::encode(workTimerRunning(), advert, sizeof(advert));

  uint8_t ids[16];
  const size_t count = objectIdsOf(advert, length, ids, sizeof(ids));

  CHECK(count == 8);
  for (size_t i = 1; i < count; i++) {
    CHECK_MSG(ids[i] >= ids[i - 1], "object ids must not go backwards");
  }
}

void testFarewellAdvert() {
  // What goes out just before deep sleep: not awake, not running, but still
  // carrying the timer so HA can tell paused from idle.
  BTHome::State state = workTimerRunning();
  state.awake = false;
  state.running = false;

  uint8_t advert[BTHome::MAX_ADVERTISEMENT];
  const size_t length = BTHome::encode(state, advert, sizeof(advert));
  CHECK(length > 0);

  const uint8_t *connectivity = findObject(advert, length, 0x19);
  const uint8_t *running = findObject(advert, length, 0x27);
  CHECK(connectivity != nullptr && connectivity[0] == 0x00);
  CHECK(running != nullptr && running[0] == 0x00);

  // The timer is still carried, so HA can tell a paused cube from an idle one.
  const uint8_t *remaining = findObject(advert, length, 0x42, 0);
  CHECK(remaining != nullptr);
  CHECK(remaining[0] != 0 || remaining[1] != 0 || remaining[2] != 0);
}

void testOutOfRangeValuesClamp() {
  BTHome::State state = workTimerRunning();
  state.remainingSeconds = -5;
  state.selectedSeconds = 100000;  // beyond what a uint24 of milliseconds holds
  state.batteryVolts = -1.0f;

  uint8_t advert[BTHome::MAX_ADVERTISEMENT];
  const size_t length = BTHome::encode(state, advert, sizeof(advert));

  // Still a well-formed advertisement of the usual size: a clamped value must
  // not wrap into something that reads as a plausible short timer.
  CHECK(length == 30);

  const uint8_t *voltage = findObject(advert, length, 0x0C);
  CHECK(voltage != nullptr && voltage[0] == 0x00 && voltage[1] == 0x00);

  const uint8_t *remaining = findObject(advert, length, 0x42, 0);
  CHECK(remaining != nullptr);
  CHECK(remaining[0] == 0x00 && remaining[1] == 0x00 && remaining[2] == 0x00);

  const uint8_t *selected = findObject(advert, length, 0x42, 1);
  CHECK(selected != nullptr);
  CHECK(selected[0] == 0xFF && selected[1] == 0xFF && selected[2] == 0xFF);
}

void testRefusesABufferItCannotFill() {
  uint8_t tooSmall[10];
  CHECK(BTHome::encode(workTimerRunning(), tooSmall, sizeof(tooSmall)) == 0);

  // And leaves it alone rather than half-writing it.
  uint8_t untouched[10];
  std::memset(untouched, 0xAA, sizeof(untouched));
  uint8_t probe[10];
  std::memset(probe, 0xAA, sizeof(probe));
  BTHome::encode(workTimerRunning(), probe, sizeof(probe));
  CHECK(std::memcmp(probe, untouched, sizeof(probe)) == 0);
}

void testFlowAdvertisesWorkWithNoSelectedLength() {
  // Flow's work face counts up, so there is no interval to report. A zero
  // Duration 2 is the sentinel for that: no fixed timer ever advertises one,
  // and with the work flag beside it a receiver can tell a stint counting up
  // from a countdown that has finished.
  BTHome::State state = workTimerRunning();
  state.work = true;
  state.remainingSeconds = 742;  // elapsed, not remaining
  state.selectedSeconds = 0;

  uint8_t advert[BTHome::MAX_ADVERTISEMENT];
  const size_t length = BTHome::encode(state, advert, sizeof(advert));
  CHECK(length > 0);

  const uint8_t *work = findObject(advert, length, 0x0F);
  CHECK(work != nullptr && work[0] == 0x01);

  const uint8_t *elapsed = findObject(advert, length, 0x42, 0);
  CHECK(elapsed != nullptr);
  CHECK(elapsed[0] == 0x70 && elapsed[1] == 0x52 && elapsed[2] == 0x0B);  // 742_000 ms

  const uint8_t *selected = findObject(advert, length, 0x42, 1);
  CHECK(selected != nullptr);
  CHECK(selected[0] == 0x00 && selected[1] == 0x00 && selected[2] == 0x00);
}

void testBreakAdvertisesNotWork() {
  BTHome::State state = workTimerRunning();
  state.work = false;

  uint8_t advert[BTHome::MAX_ADVERTISEMENT];
  const size_t length = BTHome::encode(state, advert, sizeof(advert));
  CHECK(length > 0);

  const uint8_t *work = findObject(advert, length, 0x0F);
  CHECK(work != nullptr && work[0] == 0x00);
}

// --- Sequencer -------------------------------------------------------------
// The encoder is told what packet id to write; the sequencer is what decides
// there is anything to write at all. Those are the two halves of "increments on
// change", and this is the half a receiver's deduplication depends on.

void testUnchangedStateIsNotResent() {
  BTHome::Sequencer sequencer;
  uint8_t advert[BTHome::MAX_ADVERTISEMENT];

  CHECK(sequencer.update(workTimerRunning(), advert, sizeof(advert)) > 0);
  // Same reading again: nothing for a receiver to hear.
  CHECK(sequencer.update(workTimerRunning(), advert, sizeof(advert)) == 0);
  CHECK(sequencer.update(workTimerRunning(), advert, sizeof(advert)) == 0);
}

void testPacketIdIgnoresWhatTheCallerPutInIt() {
  // The caller's packet id is not consulted -- if it were, a caller counting
  // for itself could make an unchanged reading look like a new one.
  BTHome::Sequencer sequencer;
  uint8_t advert[BTHome::MAX_ADVERTISEMENT];

  BTHome::State state = workTimerRunning();
  state.packetId = 7;
  CHECK(sequencer.update(state, advert, sizeof(advert)) > 0);
  const uint8_t *first = findObject(advert, sizeof(advert), 0x00);
  CHECK(first != nullptr && first[0] == 0);  // numbered from zero regardless

  state.packetId = 200;
  CHECK(sequencer.update(state, advert, sizeof(advert)) == 0);
}

void testPacketIdAdvancesOnlyWhenTheReadingDoes() {
  BTHome::Sequencer sequencer;
  uint8_t advert[BTHome::MAX_ADVERTISEMENT];

  BTHome::State state = workTimerRunning();
  sequencer.update(state, advert, sizeof(advert));
  const uint8_t *id = findObject(advert, sizeof(advert), 0x00);
  CHECK(id != nullptr && id[0] == 0);

  // A second off the clock is a change.
  state.remainingSeconds -= 1;
  CHECK(sequencer.update(state, advert, sizeof(advert)) > 0);
  id = findObject(advert, sizeof(advert), 0x00);
  CHECK(id != nullptr && id[0] == 1);

  // Offering the same second again is not, and does not move the id.
  CHECK(sequencer.update(state, advert, sizeof(advert)) == 0);

  state.remainingSeconds -= 1;
  CHECK(sequencer.update(state, advert, sizeof(advert)) > 0);
  id = findObject(advert, sizeof(advert), 0x00);
  CHECK(id != nullptr && id[0] == 2);
}

void testVoltageJitterBelowAMillivoltIsNotAChange() {
  // The pack voltage is a ten-reading average of a noisy ADC, so the float is
  // never quite still. What matters is whether the encoded millivolts move.
  BTHome::Sequencer sequencer;
  uint8_t advert[BTHome::MAX_ADVERTISEMENT];

  BTHome::State state = workTimerRunning();
  state.batteryVolts = 3.8200f;
  CHECK(sequencer.update(state, advert, sizeof(advert)) > 0);

  state.batteryVolts = 3.8202f;  // still 3820 mV
  CHECK(sequencer.update(state, advert, sizeof(advert)) == 0);

  state.batteryVolts = 3.8230f;  // 3823 mV
  CHECK(sequencer.update(state, advert, sizeof(advert)) > 0);
}

void testPacketIdWrapsPastAByte() {
  BTHome::Sequencer sequencer;
  uint8_t advert[BTHome::MAX_ADVERTISEMENT];

  BTHome::State state = workTimerRunning();
  // 256 distinct readings takes the id all the way round.
  for (int i = 0; i <= 256; i++) {
    state.remainingSeconds = 1500 - i;
    CHECK(sequencer.update(state, advert, sizeof(advert)) > 0);
  }

  const uint8_t *id = findObject(advert, sizeof(advert), 0x00);
  CHECK(id != nullptr && id[0] == 0);  // 256 increments from 0
}

void testFarewellClearsAwakeAndRunning() {
  // A sleeping cube is not counting, and the README's state table can only
  // describe a pause as a timer that is stopped part way through -- which needs
  // running false. The cube is always asleep while paused, so the farewell is
  // the only advertisement that can say it.
  BTHome::Sequencer sequencer;
  uint8_t advert[BTHome::MAX_ADVERTISEMENT];

  BTHome::State state = workTimerRunning();
  state.remainingSeconds = 600;
  state.selectedSeconds = 1500;
  CHECK(sequencer.update(state, advert, sizeof(advert)) > 0);

  const size_t length = sequencer.farewell(advert, sizeof(advert));
  CHECK(length > 0);

  const uint8_t *connectivity = findObject(advert, length, 0x19);
  CHECK(connectivity != nullptr && connectivity[0] == 0x00);

  const uint8_t *running = findObject(advert, length, 0x27);
  CHECK(running != nullptr && running[0] == 0x00);

  // And nothing else moves: a pause has to still say how far it got.
  const uint8_t *remaining = findObject(advert, length, 0x42, 0);
  CHECK(remaining != nullptr);
  CHECK(remaining[0] == 0xC0 && remaining[1] == 0x27 && remaining[2] == 0x09);  // 600_000 ms

  const uint8_t *selected = findObject(advert, length, 0x42, 1);
  CHECK(selected != nullptr);
  CHECK(selected[0] == 0x60 && selected[1] == 0xE3 && selected[2] == 0x16);  // 1_500_000 ms
}

void testFarewellNeedsSomethingToSayFarewellFrom() {
  // A cube that wakes on a resting face and goes straight back down has
  // published nothing, and has nothing to withdraw.
  BTHome::Sequencer sequencer;
  uint8_t advert[BTHome::MAX_ADVERTISEMENT];
  CHECK(sequencer.farewell(advert, sizeof(advert)) == 0);
}

void testFarewellIsNumberedLikeAnyOtherChange() {
  BTHome::Sequencer sequencer;
  uint8_t advert[BTHome::MAX_ADVERTISEMENT];

  CHECK(sequencer.update(workTimerRunning(), advert, sizeof(advert)) > 0);
  CHECK(sequencer.farewell(advert, sizeof(advert)) > 0);

  const uint8_t *id = findObject(advert, sizeof(advert), 0x00);
  CHECK(id != nullptr && id[0] == 1);

  // Said twice, it is only news once.
  CHECK(sequencer.farewell(advert, sizeof(advert)) == 0);
}

// --- Scheduler -------------------------------------------------------------
// When the radio goes on the air: at once for anything a receiver should hear
// promptly, and otherwise on a heartbeat.

void testTheFirstStateGoesOutAtOnce() {
  BTHome::Scheduler scheduler;
  CHECK(scheduler.due(workTimerRunning(), 5000) == BTHome::Burst::Change);
}

// The seconds and the pack voltage change all the time. They wait for the
// heartbeat, and are sent with whatever they have reached by then.
void testTheCountdownAndVoltageWaitForTheHeartbeat() {
  BTHome::Scheduler scheduler;
  BTHome::State state = workTimerRunning();
  CHECK(scheduler.due(state, 0) == BTHome::Burst::Change);

  state.remainingSeconds -= 10;
  state.batteryVolts -= 0.05f;
  CHECK(scheduler.due(state, 10000) == BTHome::Burst::None);
  CHECK(scheduler.due(state, BTHome::Scheduler::HEARTBEAT_MS - 1) == BTHome::Burst::None);
  CHECK(scheduler.due(state, BTHome::Scheduler::HEARTBEAT_MS) == BTHome::Burst::Heartbeat);

  // Counted from the heartbeat just sent, not from the start.
  CHECK(scheduler.due(state, BTHome::Scheduler::HEARTBEAT_MS + 1) == BTHome::Burst::None);
  CHECK(scheduler.due(state, 2 * BTHome::Scheduler::HEARTBEAT_MS) == BTHome::Burst::Heartbeat);
}

// An unchanged cube still says so on the heartbeat, which is what keeps a
// receiver from deciding it has gone away.
void testAnUnchangedCubeStillHasAHeartbeat() {
  BTHome::Scheduler scheduler;
  CHECK(scheduler.due(workTimerRunning(), 0) == BTHome::Burst::Change);
  CHECK(scheduler.due(workTimerRunning(), BTHome::Scheduler::HEARTBEAT_MS) ==
        BTHome::Burst::Heartbeat);
}

void testEveryPromptFieldSendsAtOnce() {
  const BTHome::State base = workTimerRunning();
  for (int field = 0; field < 5; field++) {
    BTHome::Scheduler scheduler;
    CHECK(scheduler.due(base, 0) == BTHome::Burst::Change);
    BTHome::State changed = base;
    switch (field) {
      case 0: changed.awake = false; break;
      case 1: changed.running = false; break;
      case 2: changed.work = false; break;
      case 3: changed.pomodoroCount++; break;
      case 4: changed.selectedSeconds = 300; break;
    }
    CHECK(scheduler.due(changed, 1) == BTHome::Burst::Change);
    // And a change resets the heartbeat.
    CHECK(scheduler.due(changed, BTHome::Scheduler::HEARTBEAT_MS) == BTHome::Burst::None);
  }
}
