coddingtonbear/pomodoro-cube/sim/tests/test_sleep_sequence.cpp

// The order Util::deepSleep() talks to the peripherals in. The path is a
// straight line of side effects, so the order *is* the behaviour: what it
// guards is that the farewell advertisement is on the air for the whole of the
// shutdown work, from before the panel is put away until just before the CPU
// stops, rather than being sent and cut off ahead of it.
#include <algorithm>
#include <string>
#include <vector>

#include "Arduino.h"
#include "check.h"
#include "sim_deep_sleep.h"
#include "sim_host.h"
#include "stubs.h"
#include "util.h"

namespace {

// Skips the second's pause on the sleep path. The order is what is under test,
// not the wall clock.
void noDelay(unsigned long ms) { (void)ms; }

// Runs the deep-sleep path to the point the CPU would stop, and returns the
// calls it made, with the shim's stand-in for stopping the CPU appended so
// the tests can say "before the CPU stops" in the same terms.
std::vector<std::string> sleepCalls(Util::SleepMode mode, bool announce) {
  Stubs::clear();
  SimHost::delayHook = noDelay;
  bool slept = false;
  try {
    Util::deepSleep(mode, announce);
  } catch (const SimDeepSleep &) {
    slept = true;
  }
  SimHost::delayHook = nullptr;
  CHECK(slept);
  std::vector<std::string> calls = Stubs::calls;
  calls.push_back("esp_deep_sleep_start");
  return calls;
}

long indexOf(const std::vector<std::string> &calls, const char *what) {
  const auto it = std::find(calls.begin(), calls.end(), what);
  return it == calls.end() ? -1 : (long)(it - calls.begin());
}

void checkFarewellSpansTheShutdown(const std::vector<std::string> &calls) {
  const long farewell = indexOf(calls, "BLE::farewell");
  const long shutdown = indexOf(calls, "BLE::shutdown");
  const long stop = indexOf(calls, "esp_deep_sleep_start");
  CHECK(farewell >= 0);
  CHECK(shutdown >= 0);

  // Said first: Home Assistant holds the last state it heard, and everything
  // else on this path is invisible to it.
  CHECK(farewell == 0);

  // The radio is the last thing to go, immediately before the CPU stops, so
  // the whole of the panel, pause and motor work counts as airtime for the
  // one advertisement that cannot be repeated.
  CHECK(shutdown == stop - 1);

  // Which puts every other device call between the two.
  for (const char *device :
       {"Haptic::stop", "Haptic::playBlocking", "QMI::setupWakeup", "Haptic::holdForSleep"}) {
    const long at = indexOf(calls, device);
    if (at < 0) continue;
    CHECK_MSG(farewell < at && at < shutdown, device);
  }
}

void testFarewellSpansASleepWithTheScreenOff() {
  const auto calls = sleepCalls(Util::SleepMode::Off, true);
  checkFarewellSpansTheShutdown(calls);
  const long panel = indexOf(calls, "Display::deepSleep");
  CHECK(panel > 0);
  CHECK(panel < indexOf(calls, "BLE::shutdown"));
  CHECK(indexOf(calls, "Haptic::playBlocking") >= 0);
}

// The motor is movement, and movement is what wakes the cube. Whatever it was
// playing has to be over, and the parting buzz with it, before the
// wake-on-motion detector is armed -- and the pin has to be held low after
// that, or nothing is left driving it once the CPU stops.
void testTheMotorIsQuietBeforeTheWakeIsArmed() {
  const auto calls = sleepCalls(Util::SleepMode::Off, true);
  const long stopped = indexOf(calls, "Haptic::stop");
  const long buzz = indexOf(calls, "Haptic::playBlocking");
  const long armed = indexOf(calls, "QMI::setupWakeup");
  const long held = indexOf(calls, "Haptic::holdForSleep");
  CHECK(stopped >= 0);
  CHECK(armed >= 0);
  CHECK(held >= 0);
  CHECK(stopped < buzz);
  CHECK(buzz < armed);
  CHECK(held < indexOf(calls, "esp_deep_sleep_start"));

  // The panel is put away after the buzz, not before: the second's pause that
  // follows it is the motor's time to spin down.
  CHECK(buzz < indexOf(calls, "Display::deepSleep"));
}

void testFarewellSpansASleepHoldingThePausedFrame() {
  const auto calls = sleepCalls(Util::SleepMode::Paused, false);
  checkFarewellSpansTheShutdown(calls);
  const long panel = indexOf(calls, "Display::holdPausedFrame");
  CHECK(panel > 0);
  CHECK(panel < indexOf(calls, "BLE::shutdown"));
  // No buzz asked for, so none played -- but the radio still outlasts the
  // rest of the path, and the pin is still held.
  CHECK(indexOf(calls, "Haptic::playBlocking") < 0);
  CHECK(indexOf(calls, "Haptic::holdForSleep") >= 0);
}

}  // namespace

void testSleepSequence() {
  testFarewellSpansASleepWithTheScreenOff();
  testFarewellSpansASleepHoldingThePausedFrame();
  testTheMotorIsQuietBeforeTheWakeIsArmed();
}
